Fese673/ZEGAR-ESP32/src/comms/esp_to_gution/EsptoGuitionState.h

#pragma once
#include <stdbool.h>
#include <stdint.h>

namespace EsptoGuition {

struct WeatherPayload {
  int16_t temperatureCx100 = 0;
  uint16_t humidityPctX100 = 0;
  uint16_t pressureHpaX10 = 0;
  uint16_t eco2 = 0;
  uint32_t sampleAgeMs = 0;
  uint8_t flags = 0;
  uint16_t tvoc = 0;
};

struct OutdoorWeatherPayload {
  int16_t temperatureCx100 = 0;
  uint16_t humidityPctX100 = 0;
  uint16_t pressureHpaX10 = 0;
  uint16_t windSpeedMsX100 = 0;
  uint16_t windGustMsX100 = 0;
  uint8_t windDeg = 0;
  uint8_t weatherCode = 0;
  uint8_t cloudCover = 0;
  int16_t apparentTempCx100 = 0;
  uint16_t pm25UgM3 = 0;
  uint16_t pm10UgM3 = 0;
  uint16_t co2Ppm = 0;
  uint8_t aqi = 0;
  uint8_t precipitationMmX10 = 0;
  uint8_t uvIndexX10 = 0;
  uint8_t sunriseHour = 0;
  uint8_t sunriseMin = 0;
  uint8_t sunsetHour = 0;
  uint8_t sunsetMin = 0;
  uint32_t sampleAgeMs = 0;
  uint8_t flags = 0;
  uint16_t no2UgM3 = 0;
};

struct PmsPayload {
  uint16_t pm01 = 0;
  uint16_t pm25 = 0;
  uint16_t pm10 = 0;
  uint16_t count0p3 = 0;
  uint16_t count0p5 = 0;
  uint16_t count1p0 = 0;
  uint16_t count2p5 = 0;
  uint16_t count5p0 = 0;
  uint16_t count10p0 = 0;
  uint32_t sampleAgeMs = 0;
  uint8_t flags = 0;
};

struct TimePayload {
  uint32_t unixSeconds = 0;
  uint8_t valid = 0;
};
struct SystemResourcesPayload {
  uint32_t freeRam = 0;
  uint32_t heapRam = 0;
  uint32_t dmaRam = 0;
  uint8_t core0Cpu = 0;
  uint8_t core1Cpu = 0;
  uint32_t freeFlash = 0;
  uint32_t usedFlash = 0;
  uint16_t underrunsAudio = 0;
  uint16_t overflowAudio = 0;
  uint16_t dropsAudio = 0;
  uint16_t errorsI2c = 0;
  uint16_t timeoutsI2c = 0;
};

struct WifiPayload {
  bool connected = false;
  int8_t rssi = 0;
  uint8_t ip[4] = {0, 0, 0, 0};
};

struct StatusBlePayload {
  uint8_t value; // 0 = OFF, 1 = ON+connected
};

struct StatusBellPayload {
  uint8_t value; // 0 = off, 1 = armed, 2 = ringing
};

bool buildWeatherPayload(WeatherPayload &out, unsigned long nowMs);
bool buildOutdoorWeatherPayload(OutdoorWeatherPayload &out, unsigned long nowMs);
bool buildPmsPayload(PmsPayload &out, unsigned long nowMs);
bool buildTimePayload(TimePayload &out);
bool buildWifiPayload(WifiPayload &out);
bool buildSystemResourcesPayload(SystemResourcesPayload &out);
bool buildStatusBlePayload(StatusBlePayload &out);
bool buildStatusBellPayload(StatusBellPayload &out);

void handleReceivedSettings(const uint8_t* payload, uint16_t payloadLength);
void handleReceivedMusicCommand(const uint8_t* payload, uint16_t payloadLength);
void handleReceivedMusicVolume(const uint8_t* payload, uint16_t payloadLength);
void handleReceivedMusicEQ(const uint8_t* payload, uint16_t payloadLength);
void handleReceivedMusicRequest(const uint8_t* payload, uint16_t payloadLength);
void handleReceivedRadioModeSwitch(const uint8_t* payload, uint16_t payloadLength);
void musicSettingsInit();
void musicSettingsFlush();
uint8_t getMusicVolume();

/* Etap 2: zsynchronizuj s_pendingSettings.sevenSegBrightness z NVS przy starcie.
 * Bez tego pierwszy musicSettingsFlush() (np. po zmianie innego ustawienia)
 * nadpisalby NVS defaultem 100 zamiast wartosci odczytanej. */
void setPendingSevenSegBrightness(uint8_t value);

} // namespace EsptoGuition
