Fese673/ZEGAR-ESP32/src/core/services/RtcSyncService.cpp

#include "RtcSyncService.h"

#include <Arduino.h>
#include <atomic>
#include <sys/time.h>
#include <time.h>
#include <Wire.h>

#include "AppLog.h"
#include "ClockService.h"
#include "RTCService.h"
namespace RtcSyncService {
namespace {

constexpr char TAG[] = "RTC";

static volatile bool rtcWritePending = false;
static unsigned long lastRtcWriteAttemptMillis = 0;
static unsigned long rtcWriteNotBeforeMillis = 0;
static uint8_t rtcWriteFailureCount = 0;
static std::atomic<time_t> rtcPendingEpoch{0};
static volatile unsigned long lastSeenNtpSyncMillis = 0;
static volatile bool s_clockSeeded = false;

static const char* kTzPoland = "CET-1CEST,M3.5.0,M10.5.0/3";
constexpr time_t kMinValidEpoch = 1609459200;
constexpr uint8_t kRtcRestoreAttempts = 3;
constexpr unsigned long kRtcRestoreRetryDelayMs = 2UL;

static unsigned long rtcComputeBackoffMs(uint8_t failures) {
  if (failures == 0) return 0;
  if (failures == 1) return 1000;
  if (failures == 2) return 2000;
  if (failures == 3) return 5000;
  if (failures == 4) return 10000;
  if (failures == 5) return 20000;
  return 60000;
}

static void scheduleRtcWriteFromSystemTime() {
  if (!isSystemTimeValid()) return;

  rtcPendingEpoch = time(nullptr);
  rtcWritePending = true;
  rtcWriteFailureCount = 0;
  rtcWriteNotBeforeMillis = millis() + 2000UL;
}

}  // namespace

void applyTimezone() {
  if (setenv("TZ", kTzPoland, 1) == 0) {
    tzset();
  }
}

bool isSystemTimeValid() {
  return time(nullptr) >= 1609459200;
}

bool isClockSeeded() {
  return s_clockSeeded;
}

void markClockSeeded() {
  s_clockSeeded = true;
}

void syncLocalClockFromSystemTime(int& hours, int& minutes, int& seconds) {
  const time_t now = time(nullptr);
  tm localTime;
  localtime_r(&now, &localTime);
  hours = localTime.tm_hour;
  minutes = localTime.tm_min;
  seconds = localTime.tm_sec;
}

static void tryRestoreTimeImpl(int& hours, int& minutes, int& seconds, unsigned long& lastTick);

void tryRestoreSystemTimeFromDs3231(int& hours, int& minutes, int& seconds, unsigned long& lastTick) {
  int h, m, s;
  unsigned long lt;
  tryRestoreTimeImpl(h, m, s, lt);
  hours = h;
  minutes = m;
  seconds = s;
  lastTick = lt;
}

void tryRestoreSystemTimeFromDs3231() {
  int h, m, s;
  unsigned long lt;
  tryRestoreTimeImpl(h, m, s, lt);
  Clock::set(h, m, s);
  Clock::setLastTick(lt);
}

static void tryRestoreTimeImpl(int& hours, int& minutes, int& seconds, unsigned long& lastTick) {
  // RTC przechowuje czas w UTC. System time (settimeofday) też UTC.
  // ClockService nakłada strefę czasową (CET/CEST) dla wyświetlania lokalnego.
  // nigdy nie zapisuj czasu lokalnego do DS3231.
  RTCService::Config rtcCfg;
  rtcCfg.wire = &Wire;
  rtcCfg.i2cTimeoutMs = 10;
  rtcCfg.i2cRetries = 2;
  rtcCfg.enableI2cDiagnostics = true;

  // Inicjalizacja RTC (one-shot, nie w pętli retry)
  const RTCService::Status beginStatus = RTCService::begin(rtcCfg);
  if (beginStatus == RTCService::Status::DeviceNotFound) {
    LOG_W(TAG, "DS3231 not found action=skip");
    return;
  }

  if (beginStatus == RTCService::Status::OscillatorStopped) {
    LOG_W(TAG, "DS3231 oscillator stopped action=try_epoch");
  } else if (beginStatus != RTCService::Status::Ok) {
    LOG_W(TAG, "DS3231 begin failed status=%s action=skip",
          RTCService::statusToString(beginStatus));
    return;
  } else {
    LOG_I(TAG, "DS3231 ready");
  }
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
